satria-mitra/LoRa-Rain-Gauge/Assets/Diagram/diagram.png

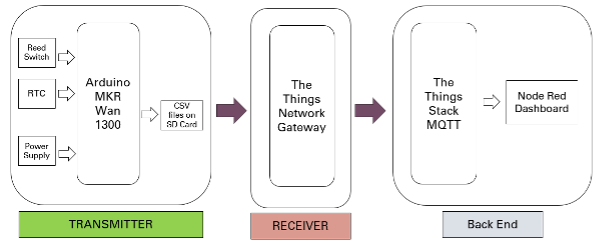
Assets/Diagram/diagram.png
