satria-mitra/LoRa-Rain-Gauge/Assets/Pictures/before_optimize.png

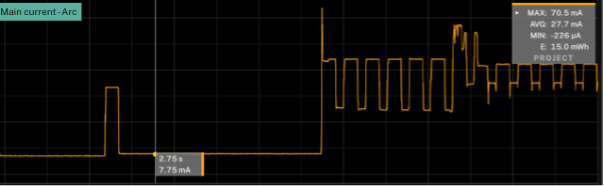
Assets/Pictures/before_optimize.png
