satria-mitra/LoRa-Rain-Gauge/Assets/Pictures/Node-red.png

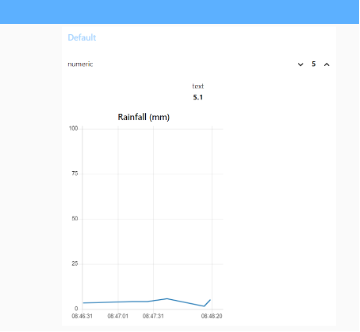
Assets/Pictures/Node-red.png
